sps-tech-lab/Force-Curve-Profiler/application/button_profile_viewer/cards_ui.pde

/*---------------------------------------
 UI Components of Cards_UI for Processing
 author: Lucas Cassiano - cassiano@mit.edu
 date: July 3rd, 2016
 lastUpdate: July 17th, 2016
 version: 1.03
 
 Controllers:
 -Button
 -ImageButton Basic
 -Tooltip
 -Slider
 -Toggle
 -Card
 -Movable Cards
 */
  //Colors
  private color c_very_dark = color(36, 37, 46);
  private color c_dark = color(29, 33, 44);
  private color c_mid = color(44, 58, 71);
  private color c_light= color(51, 64, 80);

  private color c_primary= color(33, 115, 139);
  private color c_hover = color(32, 155, 160);


  private color c_text_color = color(255);
  private color top_right = color(255);

  //Click Options
  private boolean clicked = false;
  private boolean canClick = true;

  //For text Input/Edit
  String bufferText = null;
  boolean doneText = false;

  //Default sizes
  private int s_big = 200;
  private int s_height = 30;
  private int s_med = 100;
  private int s_small = 50;

  //For Cards
  int card_h = 0;
  int card_w = 0;
  private int card_x = 0;
  private int card_y = 0;

  public void uiDark() {
    c_very_dark = color(36, 37, 46);
    c_dark = color(29, 33, 44);
    c_mid = color(44, 58, 71);
    c_light = color(51, 64, 80);
    c_hover = color(32, 155, 160);
  }

  public void uiLight() {
    c_very_dark = color(100);
    c_dark = color(150);
    c_mid = color(200);
    c_light = color(250);
    c_hover = color(32, 155, 160);
    c_text_color = color(10);
  }

  //Basic Text Button
  public boolean Button(String text, int x, int y, int w, int h) {

    if (mouseX >= x && mouseX <= x+w && 
      mouseY >= y && mouseY <= y+h) {
      fill(c_hover);
      rect(x, y, w, h);
      fill(c_text_color);
      textSize(15);
      textAlign(CENTER, CENTER);
      text(text, x, y, w, h);
      if (clicked && canClick) {
        fill(c_light);
        rect(x, y, w, h);
        text(text, x, y, w, h);
        canClick = false;
        return true;
      }
    } else {
      fill(c_light);
      rect(x, y, w, h);
      fill(c_text_color);
      textSize(15);
      textAlign(CENTER, CENTER);
      text(text, x, y, w, h);
      return false;
    }

    return false;
  }

  //Roundstyle Text Button
  public boolean Button(String text, int x, int y, int w, int h, int r) {

    if (mouseX >= x && mouseX <= x+w && 
      mouseY >= y && mouseY <= y+h) {
      fill(c_hover);
      rect(x, y, w, h, r);
      fill(c_text_color);
      textSize(15);
      textAlign(CENTER, CENTER);
      text(text, x, y, w, h);
      if (clicked && canClick) {
        fill(c_light);
        rect(x, y, w, h, r);
        text(text, x, y, w, h);
        canClick = false;
        return true;
      }
    } else {
      fill(c_light);
      rect(x, y, w, h, r);
      fill(c_text_color);
      textSize(15);
      textAlign(CENTER, CENTER);
      text(text, x, y, w, h);
      return false;
    }

    return false;
  }

  //Basic Text Button
  boolean Button(String text, int x, int y) {
    return Button(text, x, y, s_med, s_height);
  }

  //Basic Text Button
  boolean Button(String text, int x, int y, String t) {
    return Button(text, x, y, s_med, s_height, t);
  }

  //X and Y are the position of the point of the triangle
  public void Tooltip(String text, int x, int y) {
    textSize(25);
    int w = (int)textWidth(text);
    int h = 50;
    int tw = 14; //triangle width
    int th = 15; //triangle height
    noStroke();
    //Shadow
    fill(0, 0, 0, 15);
    rect(5+x-w/2, 5+y-th-h, w, h, 2);
    triangle(5+x-tw/2, 5+y-th, 5+x, 5+y, 5+x+tw/2, 5+y-th);
    //Color
    fill(c_very_dark);
    rect(x-w/2, y-th-h, w, h, 2);
    triangle(x-tw/2, y-th, x, y, x+tw/2, y-th);
    //Text
    textSize(15);
    fill(255);
    textAlign(CENTER, CENTER);
    text(text, x-w/2, y-th-h, w, h);
    //triangle(
  }

  //Button With Tooltip
  boolean Button(String text, int x, int y, int w, int h, String tooltip) {
    if (mouseX >= x && mouseX <= x+w && 
      mouseY >= y && mouseY <= y+h) {
      Tooltip(tooltip, x+w/2, y-1);
      fill(c_hover);
      rect(x, y, w, h);
      fill(c_text_color);
      textSize(15);
      textAlign(CENTER, CENTER);
      text(text, x, y, w, h);
      if (clicked && canClick) {
        fill(c_light);
        rect(x, y, w, h);
        text(text, x, y, w, h);
        canClick = false;
        return true;
      }
    } else {
      fill(c_light);
      rect(x, y, w, h);
      fill(c_text_color);
      textSize(15);
      textAlign(CENTER, CENTER);
      text(text, x, y, w, h);
      return false;
    }

    return false;
  }
  //Basic Image Button
  boolean ImageButton(PImage img, int x, int y, int w, int h) {
    if (mouseX >= x && mouseX <= x+w && 
      mouseY >= y && mouseY <= y+h) {
      fill(c_dark);
      rect(x, y, w, h);
      image(img, x, y, w, h);
      if (clicked && canClick) {
        fill(c_mid);
        rect(x, y, w, h);
        image(img, x, y, w, h);
        canClick = false;
        return true;
      }
    } else {
      fill(c_mid);
      rect(x, y, w, h);
      image(img, x, y, w, h);
      return false;
    }

    return false;
  }

  //Basic ImageButton with padding
  boolean ImageButton(PImage img, int x, int y, int w, int h, int padding) {
    if (mouseX >= x && mouseX <= x+w && 
      mouseY >= y && mouseY <= y+h) {
      fill(c_dark);
      rect(x, y, w, h);
      image(img, x+padding, y+padding, w-2*padding, h-2*padding);
      if (clicked && canClick) {
        fill(c_mid);
        rect(x, y, w, h);
        image(img, x, y, w, h);
        canClick = false;
        return true;
      }
    } else {
      fill(c_mid);
      rect(x, y, w, h);
      image(img, x+padding, y+padding, w-2*padding, h-2*padding);
      return false;
    }

    return false;
  }

  //Image Button with selected state
  boolean ImageButton(PImage img, int x, int y, int w, int h, boolean select) {
    if (select) {
      fill(c_dark);
      rect(x, y, w, h);
      image(img, x, y, w, h);
      //return true;
    } else if (mouseX >= x && mouseX <= x+w && 
      mouseY >= y && mouseY <= y+h) {
      fill(c_dark);
      rect(x, y, w, h);
      image(img, x, y, w, h);
      if (clicked && canClick) {
        fill(c_mid);
        rect(x, y, w, h);
        image(img, x, y, w, h);
        canClick = false;
        return true;
      }
    } else {
      fill(c_mid);
      rect(x, y, w, h);
      image(img, x, y, w, h);
      return false;
    }

    return false;
  }



  //ImageButton with selected state and with padding
  boolean ImageButton(PImage img, int x, int y, int w, int h, boolean select, int padding) {
    if (select) {
      fill(c_dark);
      rect(x, y, w, h);
      image(img, x+padding, y+padding, w-2*padding, h-2*padding);
      //return true;
    } else if (mouseX >= x && mouseX <= x+w && 
      mouseY >= y && mouseY <= y+h) {
      fill(c_dark);
      rect(x, y, w, h);
      image(img, x+padding, y+padding, w-2*padding, h-2*padding);
      if (clicked && canClick) {
        fill(c_mid);
        rect(x, y, w, h);
        image(img, x+padding, y+padding, w-2*padding, h-2*padding);
        canClick = false;
        return true;
      }
    } else {
      fill(c_mid);
      rect(x, y, w, h);
      image(img, x, y, w, h);
      return false;
    }

    return false;
  }


  void mousePressed() {
    clicked = true;
  }

  void mouseReleased() {
    clicked = false;
    canClick  = true;
  }

  //void keyPressed() {
  //  if (keyCode == BACKSPACE) {
  //    if (bufferText.length() > 0) {
  //      bufferText = bufferText.substring(0, bufferText.length()-1);
  //    }
  //  } else if (keyCode == DELETE) {
  //    bufferText = "";
  //  } else if (keyCode != SHIFT && keyCode != ENTER) {
  //    bufferText = bufferText + key;
  //  }

  //  if (keyCode == ' ') {
  //    bufferText = bufferText.substring(0, bufferText.length()-1);
  //    bufferText = bufferText + ' ';
  //  }


  //  if (keyCode == ENTER) {
  //    //input = myText;
  //    //bufferText = "";
  //    doneText = true;
  //  }
  //}


  private void EditText(String txt) {
    bufferText = txt;
  }
  
  public class TextInput {
    String text = "";
    boolean active = false;
    String hint = "";
    String label = "";

    public TextInput() {
    }

    public TextInput(String t) {
      this.hint = t;
    }

    public TextInput(String t, String l) {
      this.hint = t;
      this.label = l;
    }

    //Text Input
    public String draw(int x, int y, int w, int h) {
      fill(200);
      textSize(12);
      textAlign(LEFT, BOTTOM);
      text(label, x, y-21, w, 20);
      if (active) {
        //Edit Text
        fill(c_dark);
        stroke(c_light);
        rect(x, y, w, h);
        noStroke();
        fill(c_text_color);
        textSize(15);
        textAlign(CENTER, CENTER);
        text = bufferText;
        text(text, x, y, w, h);

        if (mouseX >= x && mouseX <= x+w && 
          mouseY >= y && mouseY <= y+h) {
          //Inside
        } else {
          if (clicked) {
            doneText = true;
            //canClick = true;
            active=false;
          }
        }

        if (doneText) {
          text = bufferText;
          active = false;
          doneText = false;
        }
      } else if (mouseX >= x && mouseX <= x+w && 
        mouseY >= y && mouseY <= y+h) {
        fill(c_hover);
        rect(x, y, w, h);
        fill(c_text_color);
        textSize(15);
        textAlign(CENTER, CENTER);
        text(text, x, y, w, h);
        if (clicked && canClick) {
          fill(c_light);
          rect(x, y, w, h);
          fill(255);
          text(text, x, y, w, h);
          EditText(text);
          canClick = false;
          active = true;
        }
      } else {
        fill(c_light);
        stroke(c_dark);
        rect(x, y, w, h);
        fill(c_text_color);
        textSize(15);
        textAlign(CENTER, CENTER);
        text(text, x, y, w, h);
        active = false;
      }
      if (text.length() == 0) {
        fill(150);
        textSize(15);
        textAlign(CENTER, CENTER);
        text(hint, x, y, w, h);
      }
      return text;
    }

    public String getText() {
      return text;
    }
  }


  //c_mid
  public void beginCard(String card_title, int x, int y, int w, int h) {

    noStroke();
    //Shadow
    fill(0, 0, 0, 15);
    rect(x+5, y+5, w, h);
    fill(c_light);
    rect(x, y, w, 40, 2, 2, 0, 0);
    textSize(15);
    textAlign(CENTER, CENTER);
    fill(c_text_color);
    text(card_title, x, y, w, 40);
    fill(c_mid);

    rect(x, y+40, w, h-40, 0, 0, 2, 2);

    card_h = h-40;
    card_w = w;
    card_x = x;
    card_y = y+40;
    //uiLight();
  }

  public void beginCard(int x, int y, int w, int h) {
    noStroke();
    fill(c_mid);

    rect(x, y, w, h);

    card_h = h;
    card_w = w;
    card_x = x;
    card_y = y;
    //uiDark();
  }

  public void endCard() {
    card_h = 0;
    card_w = 0;
    card_y = 0;
    card_x = 0;
  }

  //Toggle
  public boolean Toggle(boolean value, int x, int y, int w, int h) {
    fill(c_dark);
    stroke(c_light);
    rect(x, y, w, h, h/2);
    int pos = 0;
    if (value)
      pos = w-h;
    //Hover
    if (mouseX >= x && mouseX <= x+w && mouseY >= y && mouseY <= y+h)
    {

      noStroke();

      fill(red(c_hover), green(c_hover), blue(c_hover), 100);  
      ellipse(x+h/2+pos, y+h/2, h-2, h-2);
      fill(c_hover);
      ellipse(x+h/2+pos, y+h/2, h-8, h-8);
      noStroke();
      if (clicked && canClick) {
        value = !value;
        canClick = false;
        return value;
      }
    } 
    //Normal
    else {
      fill(c_light);
      stroke(c_light);
      ellipse(x+h/2+pos, y+h/2, h-8, h-8);
    }


    return value;
  }

  public boolean Toggle(boolean value, int x, int y) {
    return Toggle(value, x, y, 60, 30);
  }

  //Toggle
  public boolean RadioButton(boolean value, int x, int y, int w, int h) {
    fill(c_dark);
    stroke(c_light);
    rect(x, y, w, h, h/2);
    int pos = 0;
    if (value)
      pos = w-h;
    //Hover
    if (mouseX >= x && mouseX <= x+w && mouseY >= y && mouseY <= y+h)
    {
      fill(c_light);
      stroke(c_hover);
      ellipse(1+x+h/2+pos, y+h/2, h-2, h-2);
      noStroke();
      if (clicked && canClick) {
        value = !value;
        canClick = false;
        return value;
      }
    } 
    //Normal
    else {


      fill(c_light);
      stroke(c_light);
      ellipse(x+h/2+pos, y+h/2, h-8, h-8);
    }


    return value;
  }

  public boolean Toggle(String text, boolean value, int x, int y, int w, int h) {
    textSize(15);
    fill(255);
    textAlign(LEFT, CENTER);
    text(text, x, y, w, h);
    int pos_x = (int)textWidth(text);
    return Toggle(value, x+10+pos_x, y, 60, 30);
  }

  /*--- Slider ---
   v1.0
   */

  //Basic Slider from 0f to 1f
  public float Slider(float min, float max, float value, int x, int y, int w, int h) {
    noStroke();
    fill(c_light);
    rect(x, y+h/2, w, 4, 2);
    float pos = map(value, min, max, 0, w);
    fill(c_hover);
    rect(x, y+h/2, pos, 4, 2);

    //Hover
    if (mouseX >= x && mouseX <= x+w && mouseY >= y && mouseY <= y+h)
    {
      fill(c_hover);
      if (mousePressed) {
        pos = mouseX;
        value = map(pos, x, x+w, min, max);
        fill(red(c_hover), green(c_hover), blue(c_hover), 100);
        ellipse(pos, y+h/2, h, h); 
        fill(c_hover);
        ellipse(pos, y+h/2, h-8, h-8);
      } else {
        fill(red(c_hover), green(c_hover), blue(c_hover), 50);
        ellipse(pos+x, y+h/2, h, h); 
        fill(c_hover);
        ellipse(pos+x, y+h/2, h-8, h-8);
      }
    } 
    //Normal
    else {
      noStroke();
      fill(c_hover);
      ellipse(pos+x, y+h/2, h-8, h-8);
    }

    return value;
  }

  //Basic Slider with Tooltip
  public float Slider(float min, float max, float value, int x, int y, int w, int h, char tooltip) {
    noStroke();
    fill(c_light);
    rect(x, y+h/2, w, 4, 2);
    float pos = map(value, min, max, 0, w);
    fill(c_hover);
    rect(x, y+h/2, pos, 4, 2);

    //Hover
    if (mouseX >= x && mouseX <= x+w && mouseY >= y && mouseY <= y+h)
    {

      fill(c_hover);
      if (mousePressed) {
        stroke(c_hover);
        pos = mouseX;
        value = map(pos, x, x+w, min, max);
        fill(red(c_hover), green(c_hover), blue(c_hover), 100);
        ellipse(pos, y+h/2, h, h); 
        fill(c_hover);
        ellipse(pos, y+h/2, h-8, h-8);

        //Tooltip
        if (tooltip=='%') {
          String s = (int)(value*100)+"%";
          Tooltip(s, (int)(pos), y);
        } else if (tooltip=='#') {
          String s = str((int)value);
          Tooltip(s, (int)(pos), y);
        }
      } else {
        fill(red(c_hover), green(c_hover), blue(c_hover), 50);
        ellipse(pos+x, y+h/2, h, h); 
        fill(c_hover);
        ellipse(pos+x, y+h/2, h-8, h-8);
      }
    } 
    //Normal
    else {
      noStroke();
      fill(c_hover);
      ellipse(pos+x, y+h/2, h-8, h-8);
    }

    return value;
  }

  public float Slider(String label, float min, float max, float value, int x, int y, int w, int h) {
    int w2 = 0;
    textSize(15);
    float tw = textWidth(label);
    textSize(15);
    fill(255);
    textAlign(LEFT, CENTER);
    text(label, x, y, tw, h);
    w2 = (int)(w-tw-15);
    return Slider(min, max, value, (int)(tw+x+15), y, w2, h);
  }

  public float Slider(String label, float min, float max, float value, int x, int y, int w, int h, char tooltip) {
    int w2 = 0;
    textSize(15);
    float tw = textWidth(label);
    textSize(15);
    fill(255);
    textAlign(LEFT, CENTER);
    text(label, x, y, tw, h);
    w2 = (int)(w-tw-15);
    return Slider(min, max, value, (int)(tw+x+15), y, w2, h, tooltip);
  }

  //Minimal Slider
  public float Slider(float value, int x, int y) {
    return Slider(0f, 1f, value, x, y, s_big, s_height);
  }

  public float Slider(float value, int x, int y, char t) {
    return Slider(0f, 1f, value, x, y, s_big, s_height, t);
  }

  public float Slider(String label, float value, int x, int y) {
    return Slider(label, 0f, 1f, value, x, y, s_big, s_height);
  }

  public float Slider(String label, float value, int x, int y, char t) {
    return Slider(label, 0f, 1f, value, x, y, s_big, s_height, t);
  }
  
  public float Slider(String label, float value, int x, int y, int w, int h) {
    return Slider(label, 0f, 1f, value, x, y, w, h);
  }

  public float Slider(float value, int x, int y, int w, int h) {
    return Slider(0f, 1f, value, x, y, w, h);
  }

  public float Slider(float value, int x, int y, int w, int h, char t) {
    return Slider(0f, 1f, value, x, y, w, h, t);
  }

  public float Slider(float min, int max, int value, int x, int y, int w, int h) {
    return Slider((float) min, (float) max, value, x, y, w, h);
  }
